Stanko/retro-frame/random-backup-files/frame/frame-v2.png

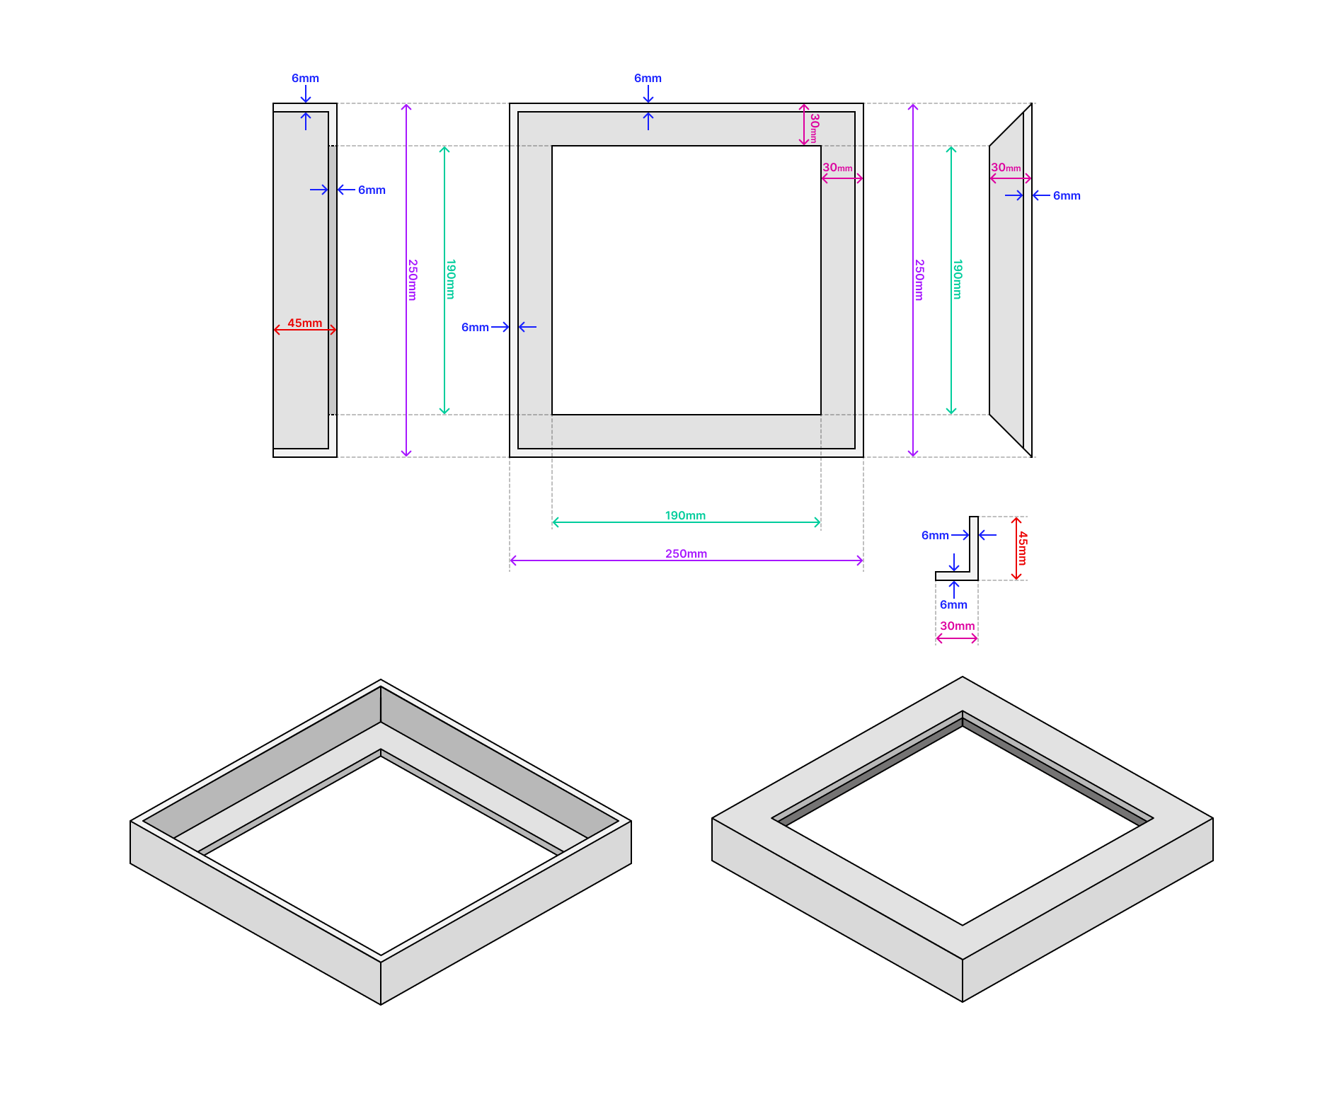
random-backup-files/frame/frame-v2.png
