Stanko/retro-frame/random-backup-files/frame/hook.png

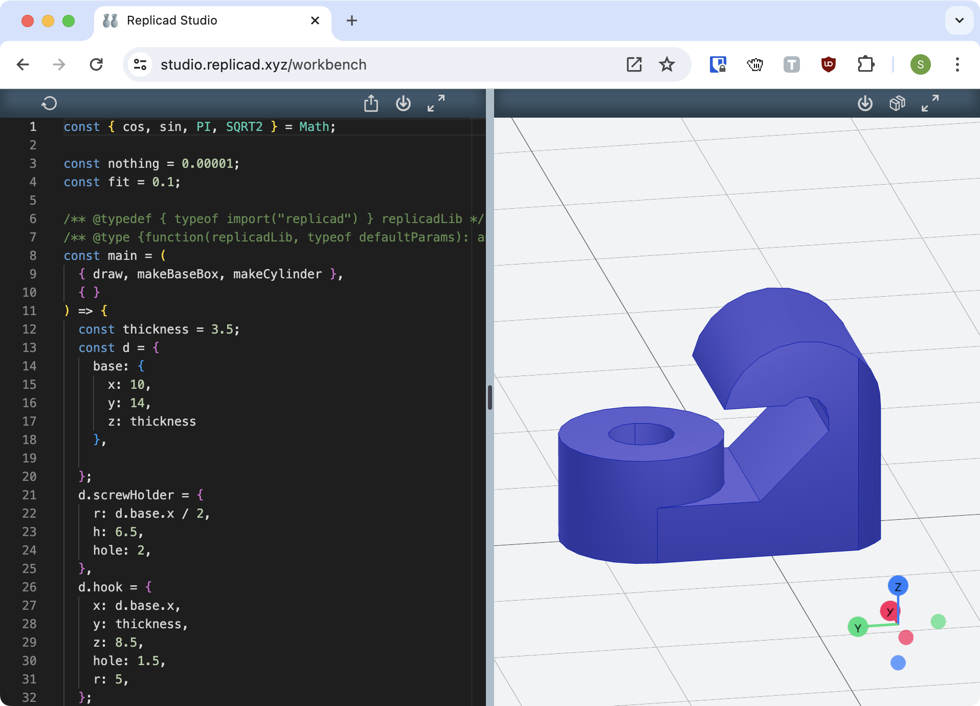
random-backup-files/frame/hook.png
