Stanko/retro-frame/code.py

# import src.diagnostics.matrix_diagnostic
# import src.diagnostics.bit_depth_diagnostic
# import src.diagnostics.font_diagnostic
# import src.diagnostics.i2c_seesaw_diagnostic
# import src.diagnostics.ui_components_diagnostic
import src.retro_frame
